CharlesLenk/cupiter/src/scad/limbs.scad

include <openscad-utilities/common.scad>
include <globals.scad>
use <robot common.scad>
use <snaps.scad>

elbow_wall_width = 1.5;

hinge_peg_h = segment_height - elbow_wall_width;

hinge_armor_y_offset = 1;
hinge_peg_d = 4;
hinge_socket_d = hinge_peg_d + 3;
hinge_peg_size = hinge_socket_d + 2.7;

function get_limb_width_at_y(
    start_width,
    end_width,
    length,
    y
) = start_width - ((start_width - end_width) / length) * y;

module limb_upper_armor_blank(
    length,
    height,
    top_width,
    top_back_length,
    bottom_front_width,
    bottom_back_width,
    joint_offset
) {
    height = height - edge_d;
    top_width = top_width - edge_d;
    bottom_width = bottom_front_width + bottom_back_width - edge_d;

    minkowski() {
        difference() {
            translate([0, edge_d/2]) {
                hull() {
                    armor_section(top_width, 0.001, height);
                    translate([top_width/4 - top_width/2, top_back_length]) {
                        armor_section(top_width/2, 0.001, height);
                    }
                    translate([-bottom_width/2 + bottom_front_width - edge_d/2, length - hinge_armor_y_offset - 0.1 - edge_d]) {
                        armor_section(bottom_width, 0.001, height, right_d = 40);
                    }
                }
            }
            translate([joint_offset, length]) {
                cylinder(d = hinge_socket_d + edge_d + 0.2, h = height, center = true);
            }
        }
        sphere(d = 1);
    }
}

module limb_lower_armor_blank(
    length,
    height,
    top_width_front,
    width_back,
    bottom_front_width,
    joint_offset
) {
    height = height - edge_d;
    top_width = top_width_front + width_back - edge_d;
    bottom_width = bottom_front_width + width_back - edge_d;

    minkowski() {
        union() {
            translate([0, edge_d/2 - hinge_armor_y_offset]) {
                hull() {
                    translate([-top_width/2 + top_width_front - edge_d/2, 0]) {
                        armor_section(x = top_width, y = 0.001, z = height, right_d = 100);
                    }
                    translate([-bottom_width/2 + bottom_front_width - edge_d/2, length + hinge_armor_y_offset - 0.1 - edge_d]) {
                        armor_section(x = bottom_width, y = 0.001, z = height, right_d = 20);
                    }
                }
            }
            translate([joint_offset, 0]) {
                cylinder(d = hinge_socket_d - edge_d, h = height, center = true);
            }
        }
        sphere(d = 1);
    }
}

module hinge_peg(is_cut = false) {
    hinge_peg_cap_d = hinge_peg_d + 1.25;
    cut_offset = is_cut ? elbow_knee_tolerance : 0;
    cap_h = (hinge_peg_cap_d - hinge_peg_d)/2;

    cylinder(d = hinge_peg_d + cut_offset, h = hinge_peg_h);
    translate([0, 0, hinge_peg_h - cap_h]) {
        cylinder(d1 = hinge_peg_d + cut_offset, d2 = hinge_peg_cap_d + cut_offset, h = cap_h);
    }
    cylinder(d2 = hinge_peg_d + cut_offset, d1 = hinge_peg_cap_d + cut_offset, h = cap_h);
}

module hinge_peg_holder(joint_offset = 0, is_cut = false) {
    if (is_cut) {
        translate([joint_offset, 0, -segment_cut_height/2]) {
            elbow_cube(true);
        }
    } else {
        translate([joint_offset, 0, -segment_height/2]) {
            cylinder(d = hinge_socket_d, h = elbow_wall_width);
            translate([0, 0, elbow_wall_width]) hinge_peg();
            difference() {
                elbow_cube();
                translate([0, 0, elbow_wall_width]) {
                    cylinder(d = hinge_socket_d + 0.6, h = segment_height);
                }
            }
        }
    }

    module elbow_cube(is_cut = false) {
        corner_d = 2.6;
        x_add = 1.4;
        y_add = 1;
        base_xy = hinge_peg_size/2;
        cube_x = base_xy + x_add;
        cube_y = base_xy + y_add;
        z = is_cut ? segment_cut_height : segment_height;

        translate([-x_add, -y_add]) cube_one_round_corner([cube_x, cube_y, z], corner_d/2);
        if (is_cut) {
            cylinder(d = hinge_socket_d + 0.1, h = z);
        }
    }
}

module hinge_socket(joint_offset = 0, is_cut = false) {
    socket_opening_angle = 100;
    if (is_cut) {
        translate([joint_offset, 0]) {
            cylinder(d = hinge_socket_d + 0.1, h = segment_cut_height, center = true);
        }
        cube([segment_cut_width, hinge_socket_d + 0.1, segment_cut_height], center = true);
    } else {
        translate([0, 0, -segment_height/2]) {
            difference() {
                union () {
                    translate([joint_offset, 0]) {
                        cylinder(d = hinge_socket_d, h = segment_height - elbow_wall_width);
                    }
                    translate([-segment_width/2, 0]) {
                        cube([segment_width, hinge_socket_d/2, segment_height]);
                    }
                }
                translate([joint_offset, 0]) {
                    fix_preview() hinge_peg(true);
                }
                fix_preview() {
                    translate([joint_offset, 0]) {
                        rotate(140) wedge(socket_opening_angle, segment_height, segment_height);
                        translate([0, 0, segment_height - elbow_wall_width]) {
                            fix_preview() cylinder(d = hinge_socket_d + 0.1, h = elbow_wall_width + 0.1);
                        }
                    }
                }
            }
        }
    }
}

module limb_segment(
    length,
    end1_len = 0,
    end2_len = 0,
    is_cut = false,
    snaps = false,
    cross_brace = false
) {
    segment_mid_y = length - end1_len - end2_len;
    height = is_cut ? segment_cut_height : segment_height;
    width = is_cut ? segment_cut_width : segment_width;

    snap_edge_dist = 1;

    max_snap_len = 5;
    snap_len = segment_mid_y - 2 * snap_edge_dist;
    exceeds_max_len = (snap_len / max_snap_len) > 2;

    end2_y = segment_mid_y > 0 ? length : end1_len + end2_len;

    if (end1_len > 0) {
        children(0);
    }
    if (end2_len > 0) {
        translate([0, end2_y, 0]) {
            rotate(180) children(1);
        }
    }

    if (segment_mid_y > 0) {
        translate([0, segment_mid_y/2 + end1_len, 0]) {
            if (cross_brace) {
                cross_brace(1, segment_width, is_cut);
            }
            difference() {
                cube([width, segment_mid_y + (is_cut ? 0.1 : 0), height], center = true);
                if (snaps) {
                    if (!exceeds_max_len) {
                        translate([0, -segment_mid_y/2 + snap_edge_dist]) {
                            armor_snap_inner_double(
                                length = snap_len,
                                target_width = segment_width,
                                is_cut = !is_cut
                            );
                        }
                    } else {
                        translate([0, -segment_mid_y/2 + snap_edge_dist]) {
                            armor_snap_inner_double(
                                length = max_snap_len,
                                target_width = segment_width,
                                is_cut = !is_cut
                            );
                        }
                        translate([0, -max_snap_len - snap_edge_dist + segment_mid_y/2]) {
                            armor_snap_inner_double(
                                length = max_snap_len,
                                target_width = segment_width,
                                is_cut = !is_cut
                            );
                        }
                    }
                }
            }
        }
    }
}
